jellehierck/bee-buttons-ros/Code/Button/include/lights.h

#pragma once 


void leds_setup();
void leds_loop();
void CircleMode(String color);
void Clear();
void FullMode(String color);
void Rainbow();
void BlinkMode(String color);
void set_brightness(int brightness);
void Show_Bat();
