jellehierck/bee-buttons-ros/Code/Button/include/painlessmeshfiles.h

#pragma once 



void receivedCallback(uint32_t from, String &msg);
void newConnectionCallback(uint32_t nodeId);
void changedConnectionCallback();
void nodeTimeAdjustedCallback(int32_t offset);
void delayReceivedCallback(uint32_t from, int32_t delay);

void painlessmesh_setup();
void mesh_loop();

void send_message_host(String message);
